haphucc/PBL5_AIoT/Model_AI_Face_recognize/Face_img/Phuc/0.jpg

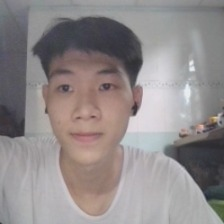
Model_AI_Face_recognize/Face_img/Phuc/0.jpg
