haphucc/PBL5_AIoT/Model_AI_Face_recognize/Face_img/Phuc/87.jpg

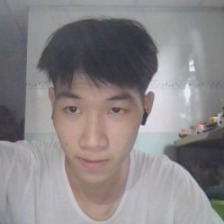
Model_AI_Face_recognize/Face_img/Phuc/87.jpg
