haphucc/PBL5_AIoT/Model_AI_Face_recognize/Face_img/Ronaldo/ronaldo.jpg

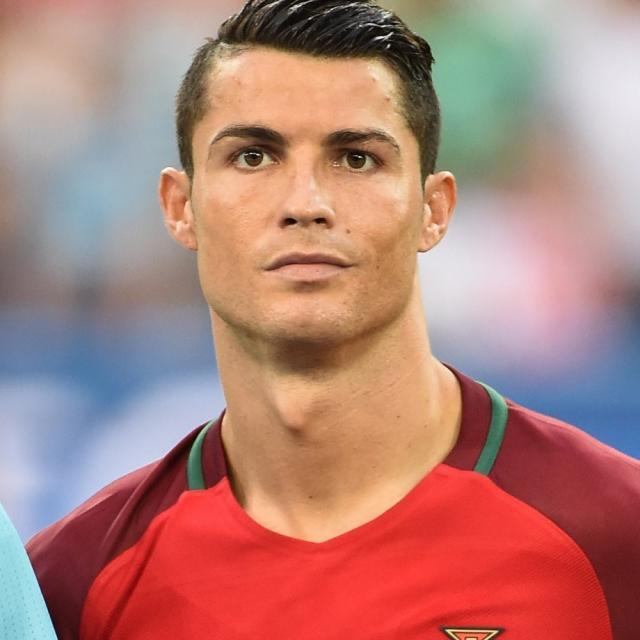
Model_AI_Face_recognize/Face_img/Ronaldo/ronaldo.jpg
