haphucc/PBL5_AIoT/PCB_Mach_Nguon/mach_nguon_PCB_2D_pbl5.jpg

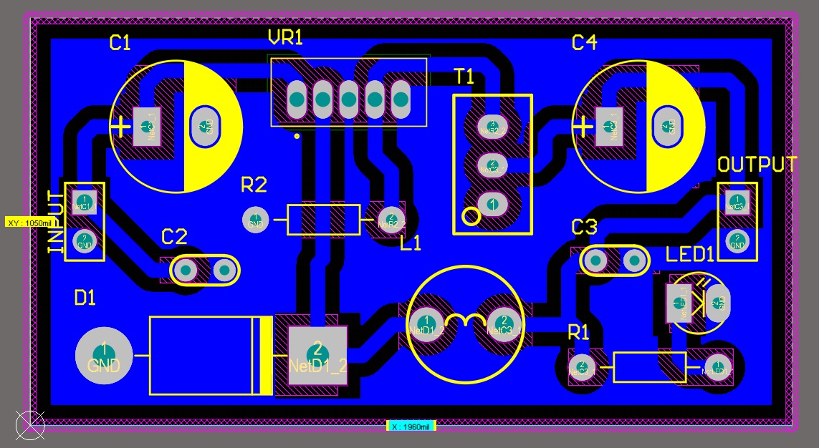
PCB_Mach_Nguon/mach_nguon_PCB_2D_pbl5.jpg
